I-elshamy/6DOF-Robot-Arm/CAD/Solidoworks/Full_aseembly.SLDASM

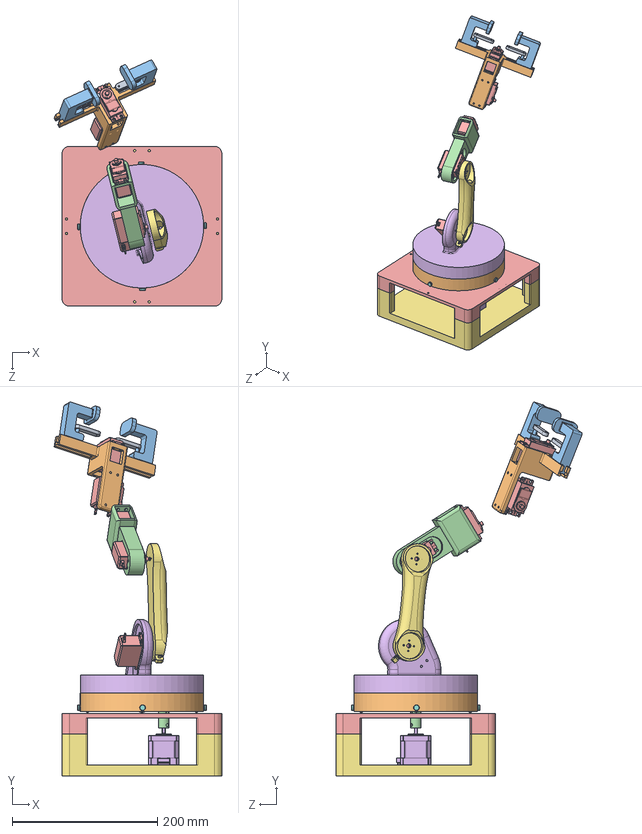
[picture p31: CAD file, 2026-05-20]
CAD/Solidoworks/Full_aseembly.SLDASM
230.9 x 514.8 x 339.1 mm
lower base
Nima 17 40x42x5mm
upper base
coupler
spur gear_am
Internal_gear
instrument ball bearing_68_am x 4
pin x 4
Arm 01
cap
servo_without_face x 5
link2_us (1)
Gripper Armx2 x 2
Servo holder
Servo_Arm_link x 2
