I-elshamy/6DOF-Robot-Arm/CAD/Solidoworks/Gear_guide.SLDPRT

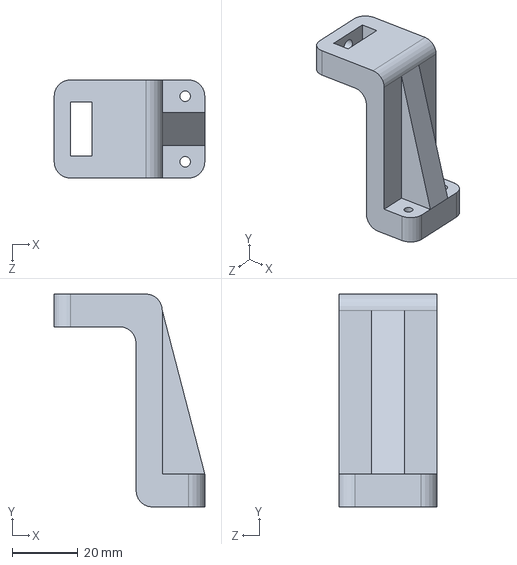
[picture p46: CAD file, 2026-05-20]
CAD/Solidoworks/Gear_guide.SLDPRT
46.0 x 65.0 x 30.0 mm
