I-elshamy/6DOF-Robot-Arm/CAD/STL/Gripper Arm(x2).STL

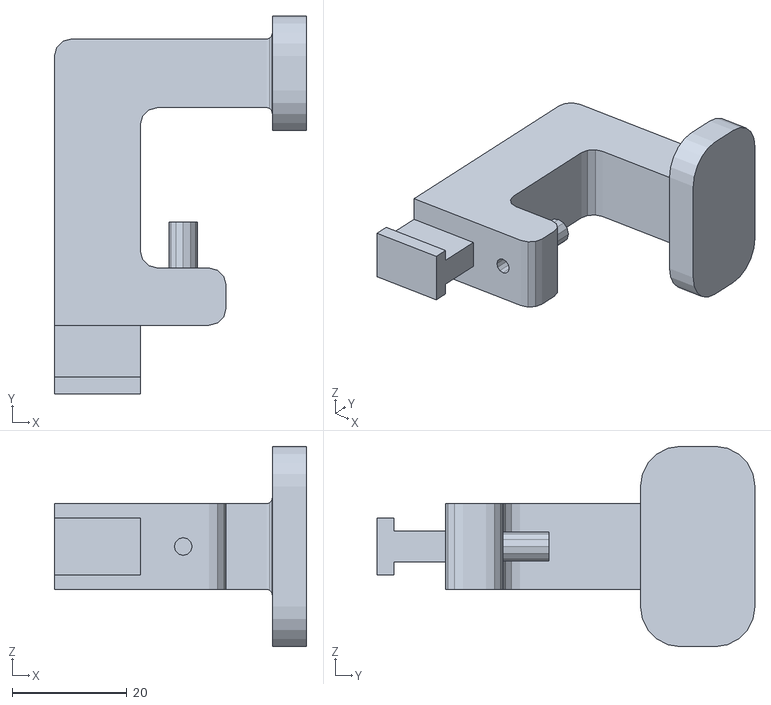
[picture p47: CAD file, 2026-05-20]
CAD/STL/Gripper Arm(x2).STL
44.1 x 66.0 x 35.0
