I-elshamy/6DOF-Robot-Arm/matlab/Internal_gear_Default_sldprt.STEP

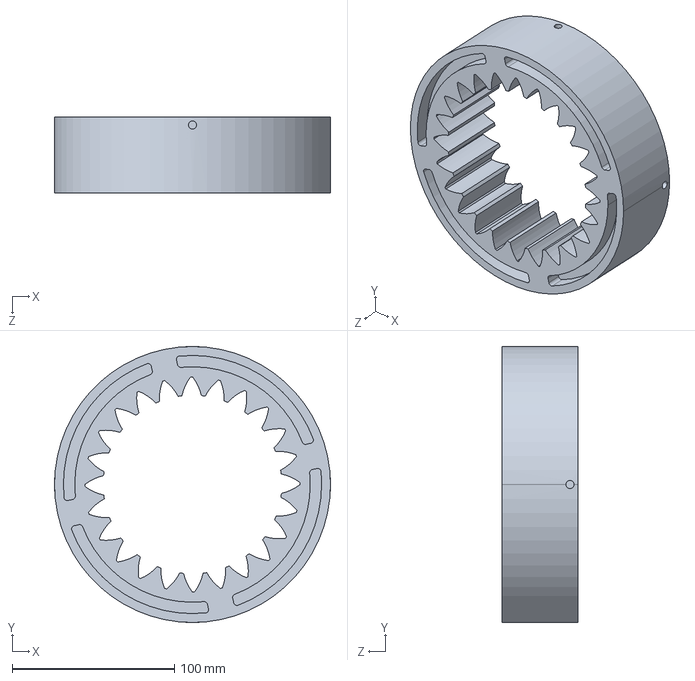
[picture p48: CAD file, 2026-05-20]
matlab/Internal_gear_Default_sldprt.STEP
170.0 x 170.0 x 47.0 mm
