I-elshamy/6DOF-Robot-Arm/CAD/Solidoworks/Internal_gear.SLDPRT

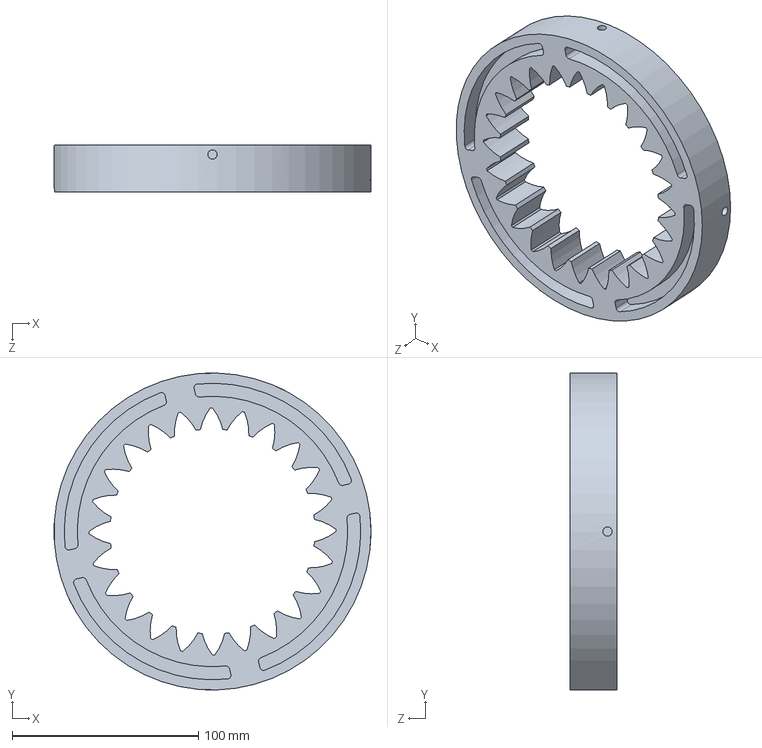
[picture p49: CAD file, 2026-05-20]
CAD/Solidoworks/Internal_gear.SLDPRT
170.0 x 170.0 x 25.0 mm
