I-elshamy/6DOF-Robot-Arm/CAD/STL/spur gear_with_shaft.STL

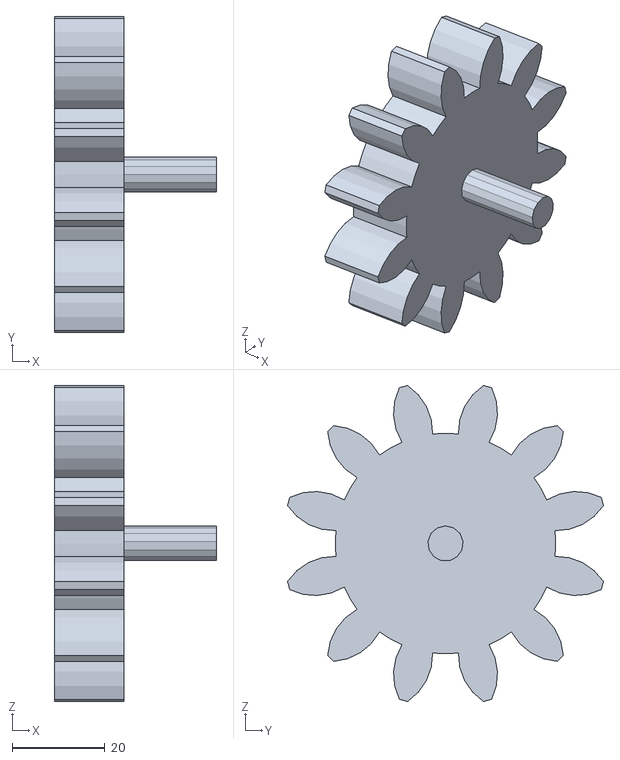
[picture p50: CAD file, 2026-05-20]
CAD/STL/spur gear_with_shaft.STL
35.0 x 68.1 x 68.1
