I-elshamy/6DOF-Robot-Arm/matlab/link2_us_Default_sldprt.STEP

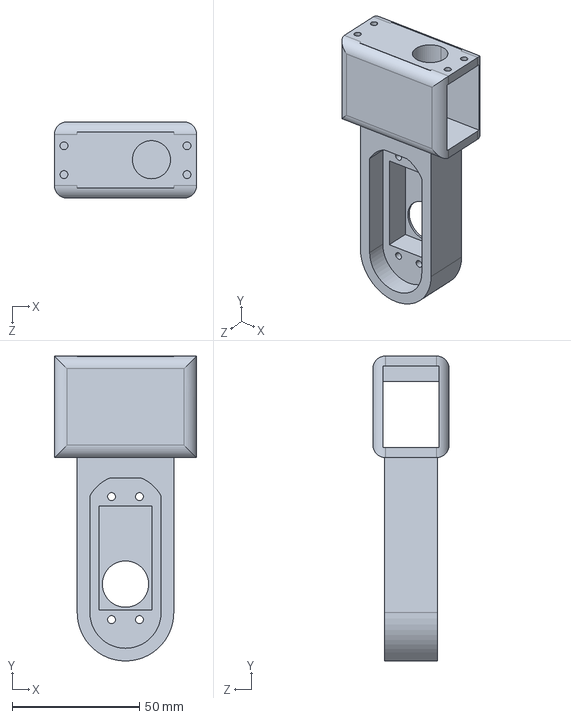
[picture p51: CAD file, 2026-05-20]
matlab/link2_us_Default_sldprt.STEP
56.0 x 120.0 x 30.0 mm
