I-elshamy/6DOF-Robot-Arm/robot_arm/src/arm_description/meshes/end_effector_link.STL

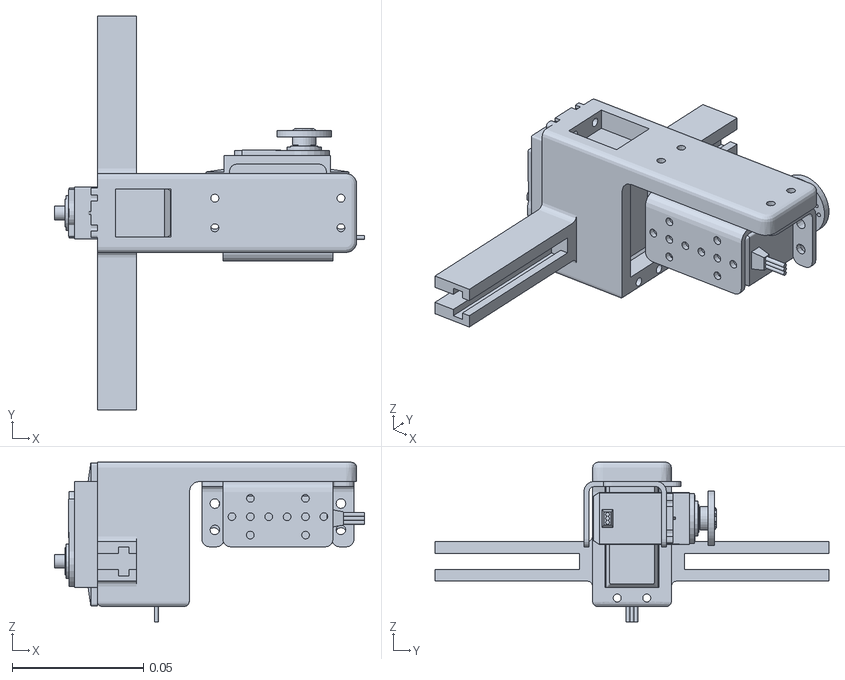
[picture p52: CAD file, 2026-05-18]
robot_arm/src/arm_description/meshes/end_effector_link.STL
0.118 x 0.15 x 0.0607
