I-elshamy/6DOF-Robot-Arm/robot_arm/src/arm_description/meshes/gears_link.STL

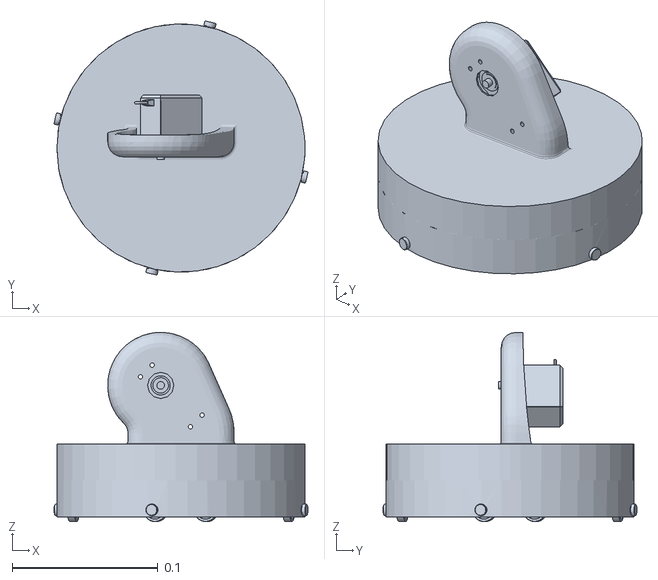
[picture p53: CAD file, 2026-05-18]
robot_arm/src/arm_description/meshes/gears_link.STL
0.174 x 0.174 x 0.13
