I-elshamy/6DOF-Robot-Arm/robot_arm/src/arm_description/meshes/bracket_1.STL

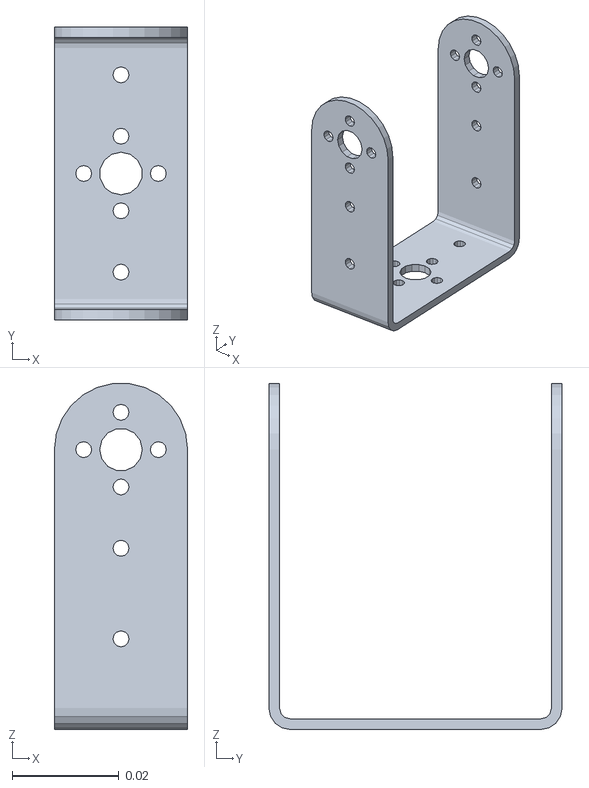
[picture p54: CAD file, 2026-05-18]
robot_arm/src/arm_description/meshes/bracket_1.STL
0.025 x 0.055 x 0.0649
