I-elshamy/6DOF-Robot-Arm/CAD/Solidoworks/mg996_arm_2pad.step

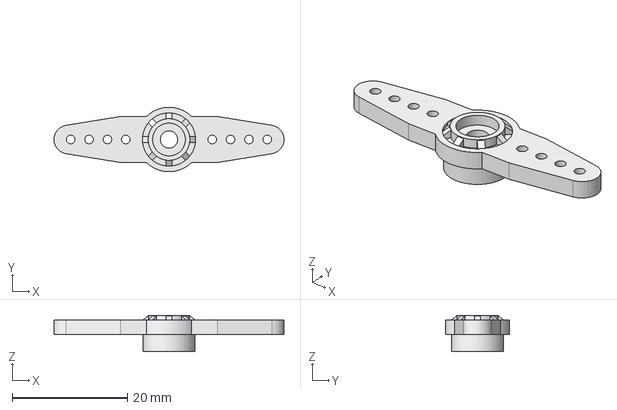
[picture p55: CAD file, 2026-05-20]
CAD/Solidoworks/mg996_arm_2pad.step
40.0 x 11.2 x 6.30 mm
