I-elshamy/6DOF-Robot-Arm/CAD/Solidoworks/mg996_arm_round.step

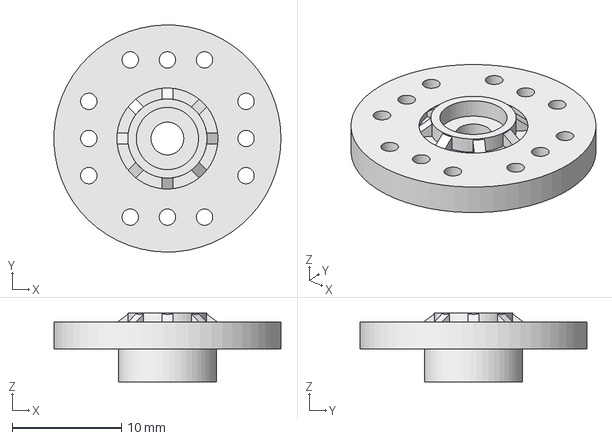
[picture p56: CAD file, 2026-05-20]
CAD/Solidoworks/mg996_arm_round.step
20.8 x 20.8 x 6.30 mm
