I-elshamy/6DOF-Robot-Arm/CAD/STL/upper base.STL

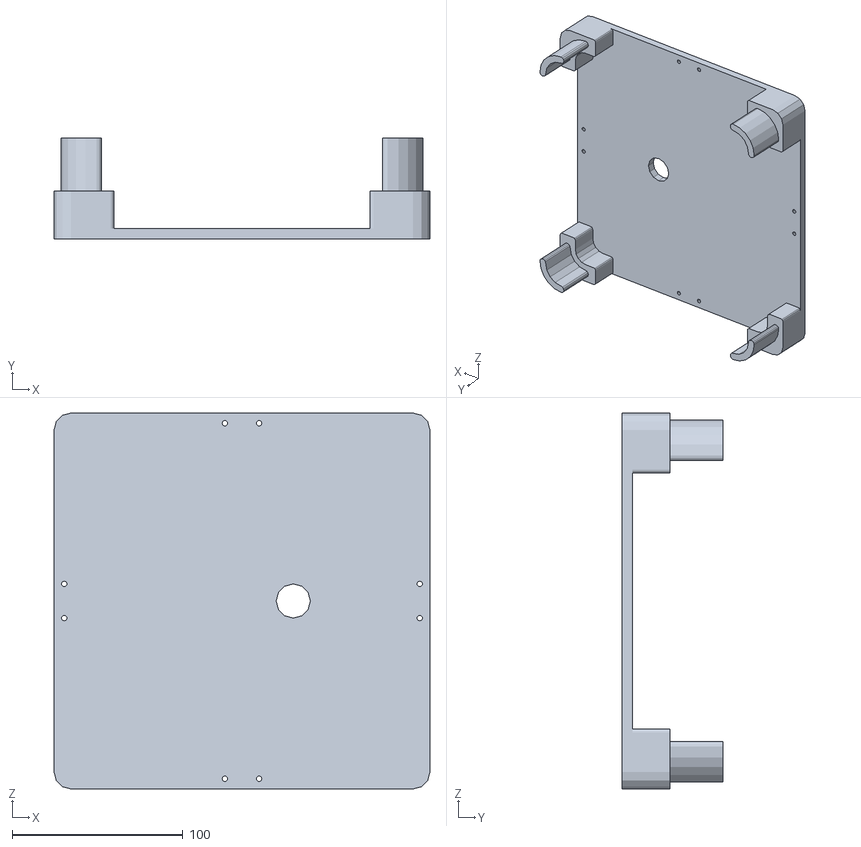
[picture p57: CAD file, 2026-05-20]
CAD/STL/upper base.STL
220.0 x 59.0 x 220.0
