I-elshamy/6DOF-Robot-Arm/CAD/STL/Servo_Arm_link(x2).STL

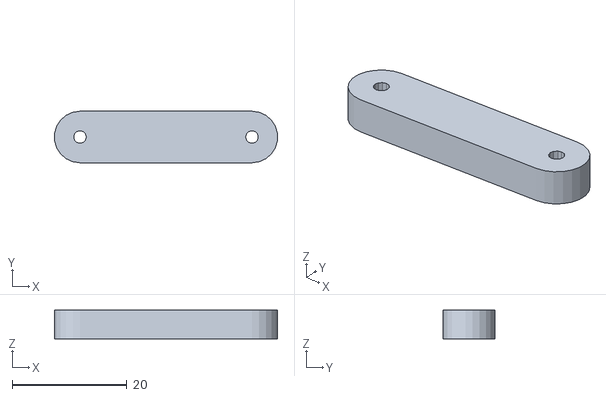
[picture p58: CAD file, 2026-05-20]
CAD/STL/Servo_Arm_link(x2).STL
38.9 x 9.00 x 5.00
