I-elshamy/6DOF-Robot-Arm/CAD/Solidoworks/servo_without_face.SLDPRT

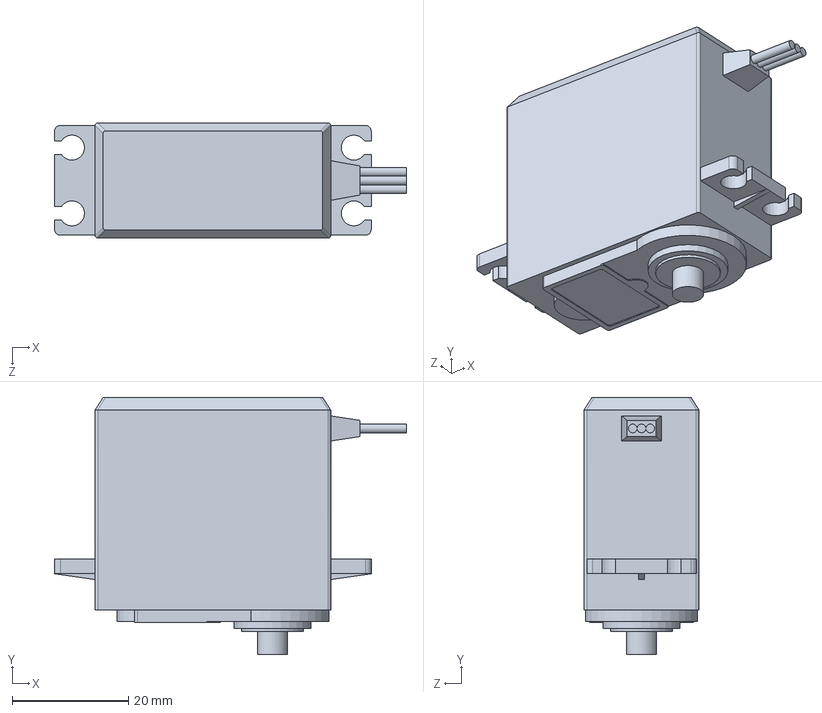
[picture p59: CAD file, 2026-05-20]
CAD/Solidoworks/servo_without_face.SLDPRT
60.5 x 44.2 x 19.8 mm
