I-elshamy/6DOF-Robot-Arm/CAD/Solidoworks/Nima 17 40x42x5mm.SLDPRT

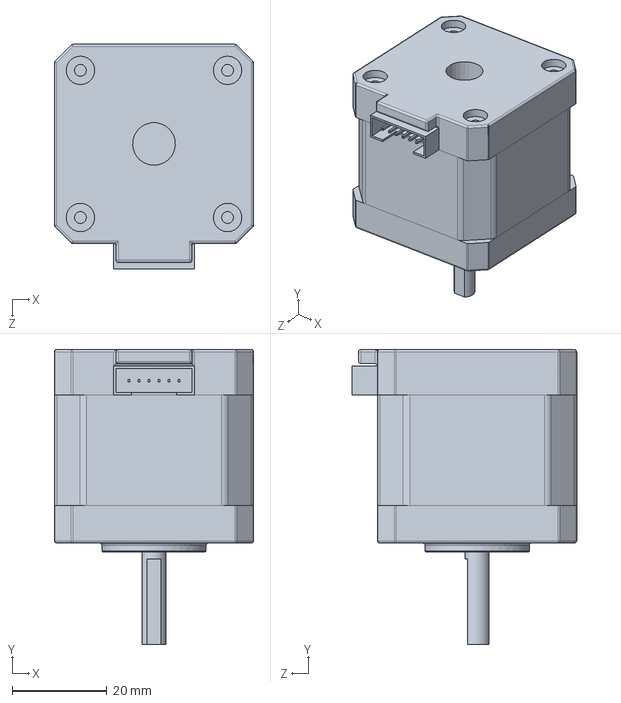
[picture p60: CAD file, 2026-05-20]
CAD/Solidoworks/Nima 17 40x42x5mm.SLDPRT
42.0 x 62.2 x 47.3 mm
