I-elshamy/6DOF-Robot-Arm/CAD/Solidoworks/instrument ball bearing_68_am.sldprt

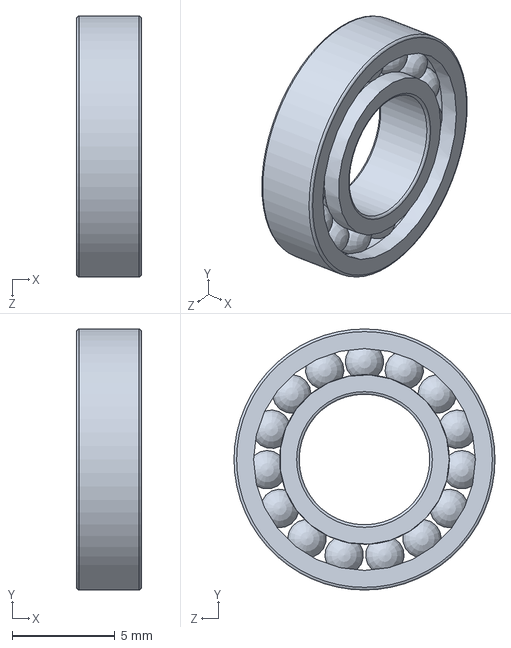
[picture p61: CAD file, 2026-05-20]
CAD/Solidoworks/instrument ball bearing_68_am.sldprt
3.17 x 12.7 x 12.7 mm
