I-elshamy/6DOF-Robot-Arm/CAD/Solidoworks/coupler.SLDPRT

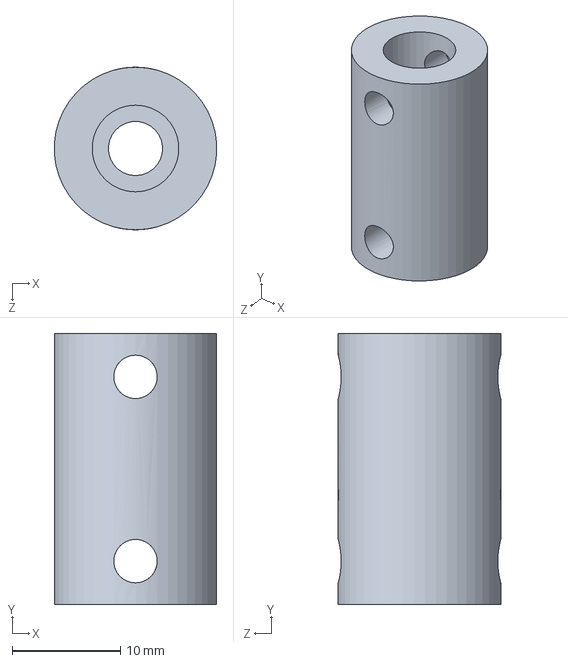
[picture p62: CAD file, 2026-05-20]
CAD/Solidoworks/coupler.SLDPRT
15.0 x 25.0 x 15.0 mm
