I-elshamy/6DOF-Robot-Arm/matlab/trajectory_servo_control_ert_rtw/trajectory_servo_control_types.h

/*
 * File: trajectory_servo_control_types.h
 *
 * Code generated for Simulink model 'trajectory_servo_control'.
 *
 * Model version                  : 1.4
 * Simulink Coder version         : 24.1 (R2024a) 19-Nov-2023
 * C/C++ source code generated on : Mon May 18 10:21:15 2026
 *
 * Target selection: ert.tlc
 * Embedded hardware selection: ARM Compatible->ARM Cortex
 * Code generation objectives: Unspecified
 * Validation result: Not run
 */

#ifndef trajectory_servo_control_types_h_
#define trajectory_servo_control_types_h_
#include "rtwtypes.h"
#ifndef struct_tag_9aqKbsbsI7JI0RwgnVwU0C
#define struct_tag_9aqKbsbsI7JI0RwgnVwU0C

struct tag_9aqKbsbsI7JI0RwgnVwU0C
{
  int32_T __dummy;
};

#endif                                 /* struct_tag_9aqKbsbsI7JI0RwgnVwU0C */

#ifndef typedef_b_arduinodriver_ArduinoDigita_T
#define typedef_b_arduinodriver_ArduinoDigita_T

typedef struct tag_9aqKbsbsI7JI0RwgnVwU0C b_arduinodriver_ArduinoDigita_T;

#endif                             /* typedef_b_arduinodriver_ArduinoDigita_T */

#ifndef struct_tag_qrLkTWTW64zZK0sqwALTyG
#define struct_tag_qrLkTWTW64zZK0sqwALTyG

struct tag_qrLkTWTW64zZK0sqwALTyG
{
  boolean_T matlabCodegenIsDeleted;
  int32_T isInitialized;
  boolean_T isSetupComplete;
  b_arduinodriver_ArduinoDigita_T DigitalIODriverObj;
};

#endif                                 /* struct_tag_qrLkTWTW64zZK0sqwALTyG */

#ifndef typedef_codertarget_arduinobase_block_T
#define typedef_codertarget_arduinobase_block_T

typedef struct tag_qrLkTWTW64zZK0sqwALTyG codertarget_arduinobase_block_T;

#endif                             /* typedef_codertarget_arduinobase_block_T */

#ifndef struct_tag_VzK3jWyzjz6OGczb4jMFhG
#define struct_tag_VzK3jWyzjz6OGczb4jMFhG

struct tag_VzK3jWyzjz6OGczb4jMFhG
{
  boolean_T matlabCodegenIsDeleted;
  int32_T isInitialized;
  boolean_T isSetupComplete;
};

#endif                                 /* struct_tag_VzK3jWyzjz6OGczb4jMFhG */

#ifndef typedef_codertarget_arduinobase_inter_T
#define typedef_codertarget_arduinobase_inter_T

typedef struct tag_VzK3jWyzjz6OGczb4jMFhG codertarget_arduinobase_inter_T;

#endif                             /* typedef_codertarget_arduinobase_inter_T */

/* Parameters (default storage) */
typedef struct P_trajectory_servo_control_T_ P_trajectory_servo_control_T;

/* Forward declaration for rtModel */
typedef struct tag_RTM_trajectory_servo_cont_T RT_MODEL_trajectory_servo_con_T;

#endif                                 /* trajectory_servo_control_types_h_ */

/*
 * File trailer for generated code.
 *
 * [EOF]
 */
