I-elshamy/6DOF-Robot-Arm/matlab/trajectory_servo_control_ert_rtw/ext_mode_types.h

/*
 * ext_mode_types.h
 *
 * Code generation for model "trajectory_servo_control".
 *
 * Model version              : 1.4
 * Simulink Coder version : 24.1 (R2024a) 19-Nov-2023
 * C source code generated on : Mon May 18 10:21:15 2026
 *
 * Target selection: ert.tlc
 * Embedded hardware selection: ARM Compatible->ARM Cortex
 * Code generation objectives: Unspecified
 * Validation result: Not run
 */

#ifndef EXT_MODE_TYPES_H
#define EXT_MODE_TYPES_H
#include "rtwtypes.h"

/** External Mode Event ID */
typedef uint16_T extmodeEventId_T;

/** External Mode real time, measured using the target's clock */
typedef uint32_T extmodeRealTime_T;

/** External Mode simulation time */
typedef time_T extmodeSimulationTime_T;

/** External Mode double data type */
typedef real_T extmodeDouble_T;

/** External Mode classic trigger signal */
typedef real_T extmodeClassicTriggerSignal_T;

/** Run the simulation forever (infinite simulation end time) */
#define EXTMODE_SIMULATION_RUN_FOREVER ((extmodeSimulationTime_T) -1)

/* Define max value of 32-bit unsigned type */
#define XCP_UINT32_MAX                 0xFFFFFFFFU

/** External Mode Base rate event id */
#define EXTMODE_BASE_RATE_EVENT_ID     0

/** External Mode Max Event Id */
#define EXTMODE_MAX_EVENT_ID           0xFF
#endif                                 /* EXT_MODE_TYPES_H */

/* [EOF] ext_mode_types.h */
