I-elshamy/6DOF-Robot-Arm/robot_arm/src/moveit_trial/config/joint_limits.yaml

# joint_limits.yaml allows the dynamics properties specified in the URDF to be overwritten or augmented as needed

# For beginners, we downscale velocity and acceleration limits.
# You can always specify higher scaling factors (<= 4.0) in your motion requests.  # Increase the values below to 4.0 to always move at maximum speed.
default_velocity_scaling_factor: 0.5
default_acceleration_scaling_factor: 0.5

# Specific joint properties can be changed with the keys [max_position, min_position, max_velocity, max_acceleration]
# Joint limits can be turned off with [has_velocity_limits, has_acceleration_limits]
joint_limits:
  bracket_1_joint:
    has_velocity_limits: true
    max_velocity: 4.0
    has_acceleration_limits: true
    max_acceleration: 4.0
  end_effector_joint:
    has_velocity_limits: true
    max_velocity: 4.0
    has_acceleration_limits: true
    max_acceleration: 4.0
  joint_1:
    has_velocity_limits: true
    max_velocity: 4.0
    has_acceleration_limits: true
    max_acceleration: 4.0
  joint_2:
    has_velocity_limits: true
    max_velocity: 4.0
    has_acceleration_limits: true
    max_acceleration: 4.0
  stepper_joint:
    has_velocity_limits: true
    max_velocity: 4.0
    has_acceleration_limits: true
    max_acceleration: 4.0
