I-elshamy/6DOF-Robot-Arm/robot_arm/src/moveit_trial/config/initial_positions.yaml

# Default initial positions for robot_arm's ros2_control fake system

initial_positions:
  bracket_1_joint: 0
  end_effector_joint: 0
  joint_1: 0
  joint_2: 0
  stepper_joint: 0
